tskauli/MorseMachine/[Originals]/DSC04385_cr_exp.jpg

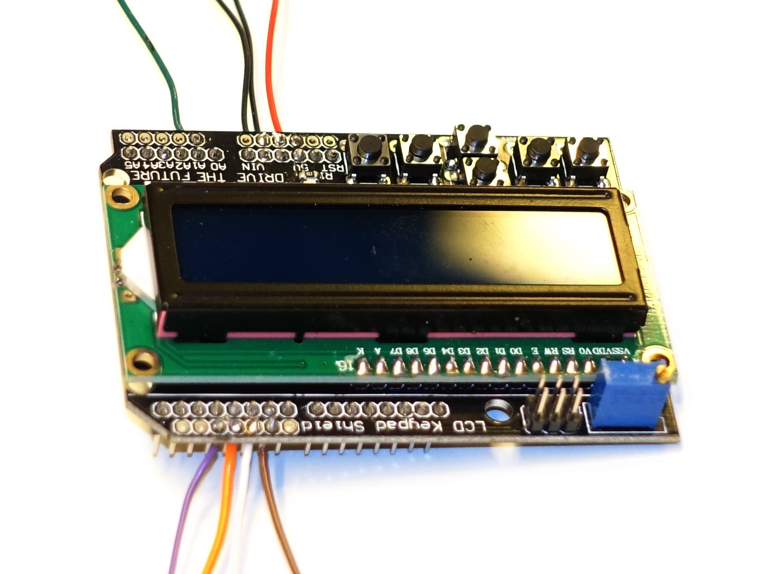
[Originals]/DSC04385_cr_exp.jpg
