tskauli/MorseMachine/[Originals]/DSC04387_cr_exp.JPG

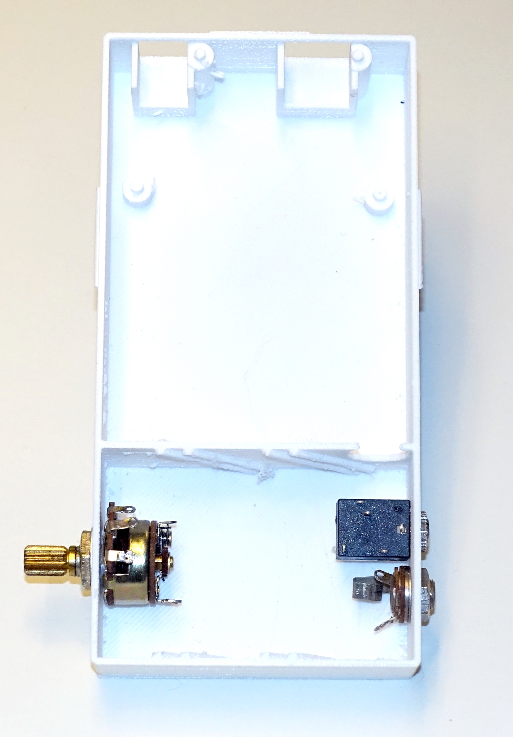
[Originals]/DSC04387_cr_exp.JPG
