tskauli/MorseMachine/DSC04356.JPG

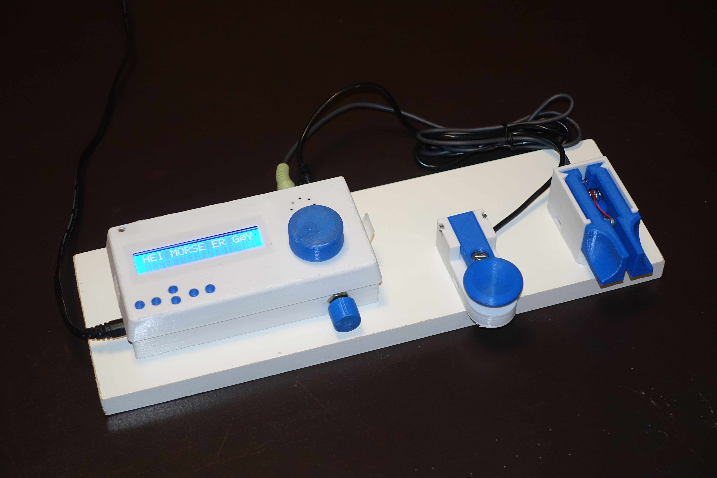
DSC04356.JPG
