tskauli/MorseMachine/DSC04356_cr_exp MorseMachine.jpg

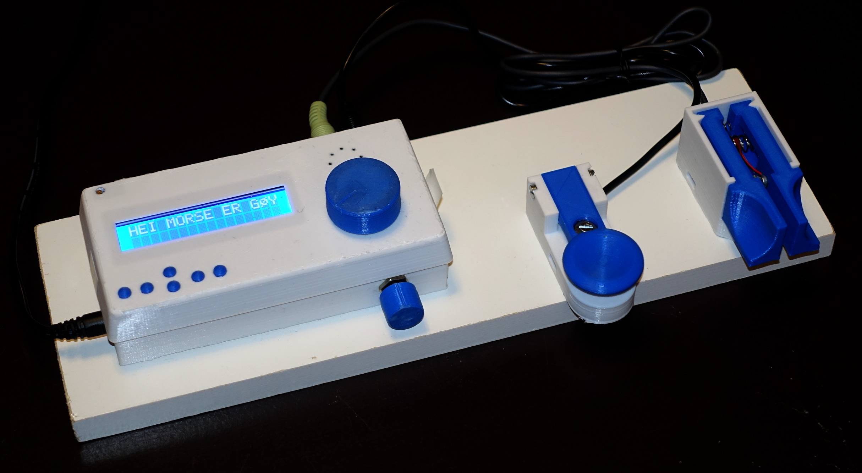
DSC04356_cr_exp MorseMachine.jpg
