tskauli/MorseMachine/DSC04385.JPG

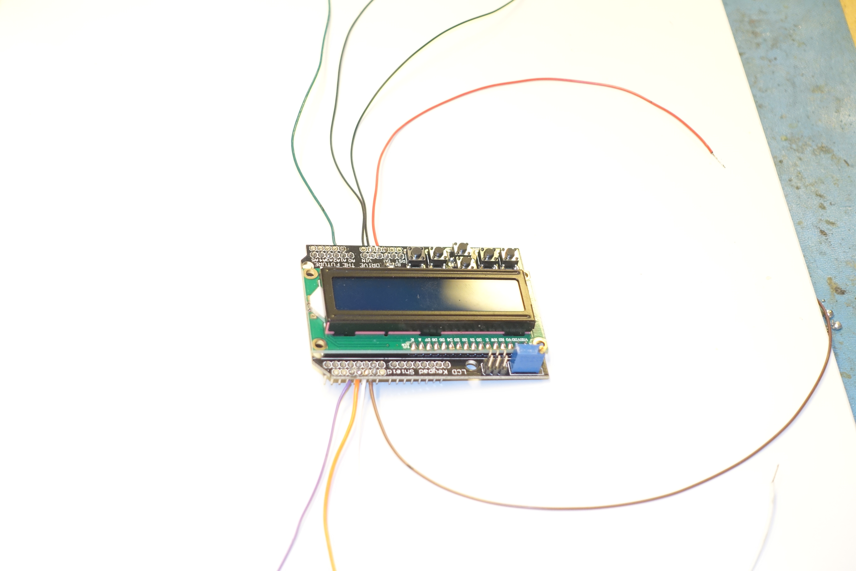
DSC04385.JPG
