tskauli/MorseMachine/DSC04387.JPG

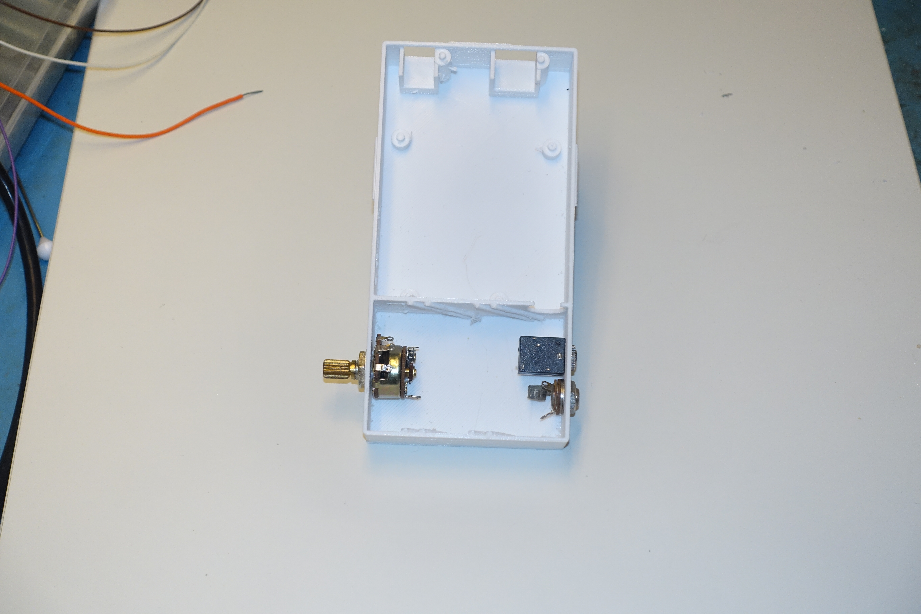
DSC04387.JPG
