tskauli/MorseMachine/DSC04387_cr_exp.JPG

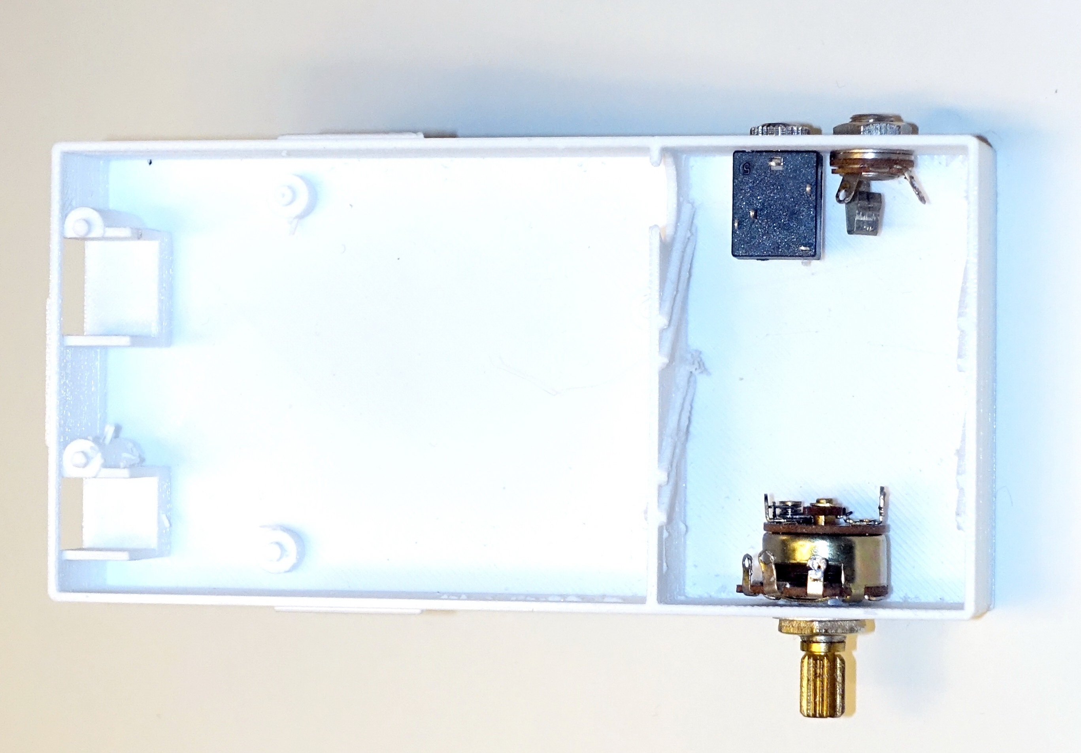
DSC04387_cr_exp.JPG
