tskauli/MorseMachine/DSC04388.JPG

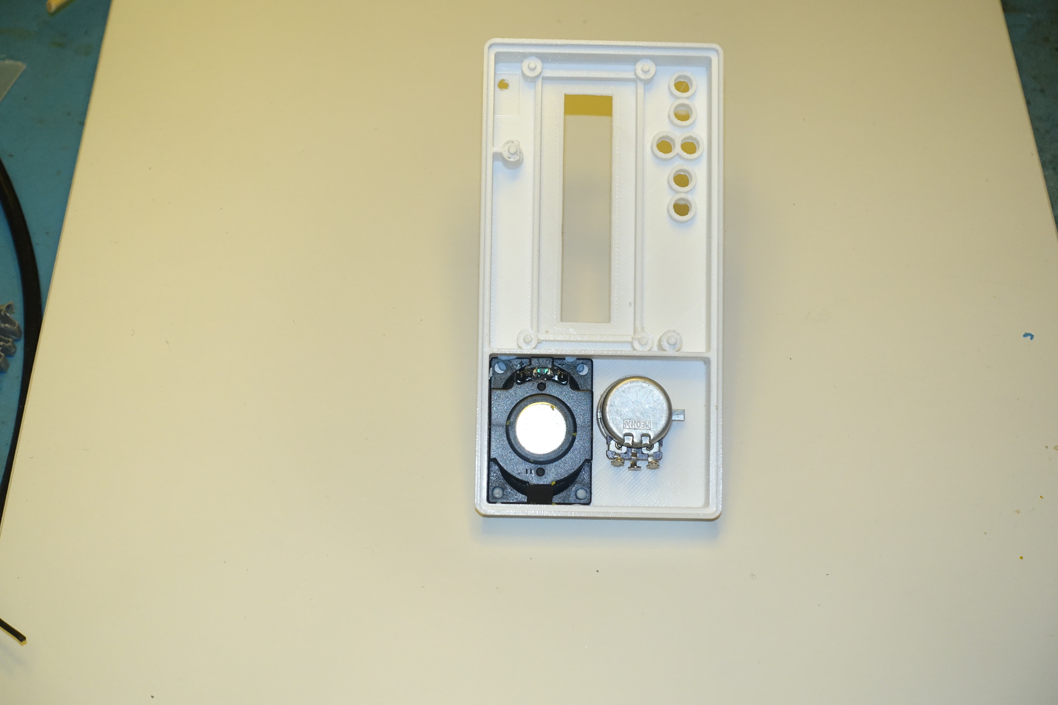
DSC04388.JPG
