tskauli/MorseMachine/DSC04390.JPG

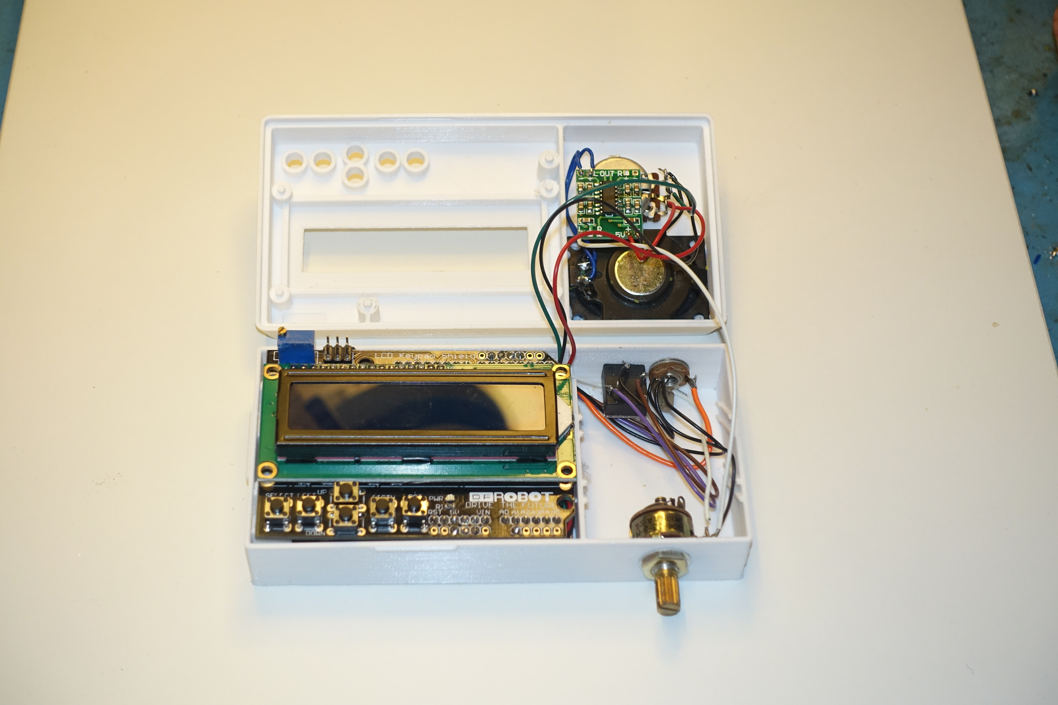
DSC04390.JPG
