tskauli/MorseMachine/DSC04390_cr_exp.jpg

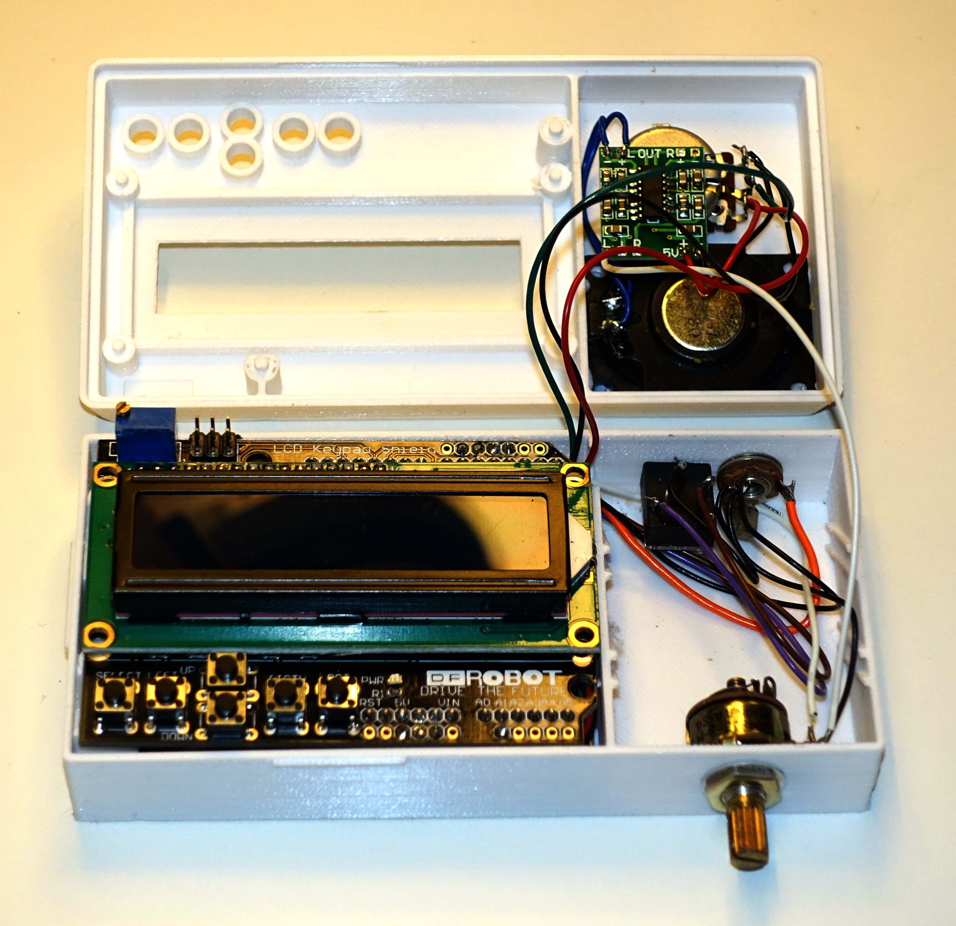
DSC04390_cr_exp.jpg
