tskauli/MorseMachine/DSC09773_cr_exp.JPG

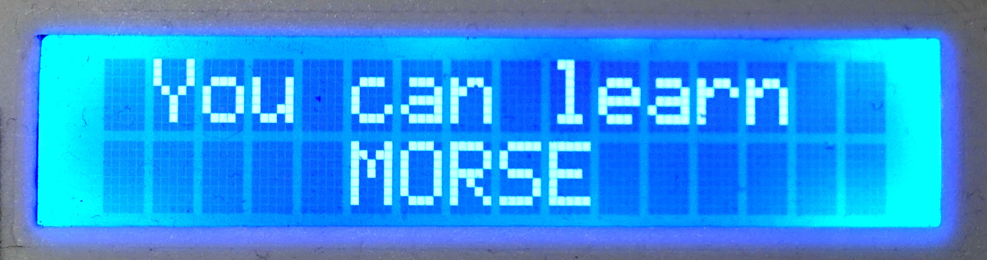
DSC09773_cr_exp.JPG
